Xenii1642/Xii-Boy-Pocket/STL/Buttons/R.stl

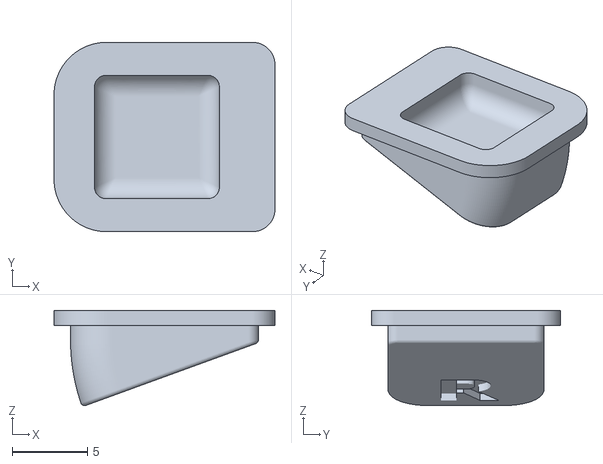
[picture p18: CAD file, 2024-10-31]
STL/Buttons/R.stl
14.7 x 12.6 x 6.34
