Xenii1642/Xii-Boy-Pocket/STL/Buttons/Volume.stl

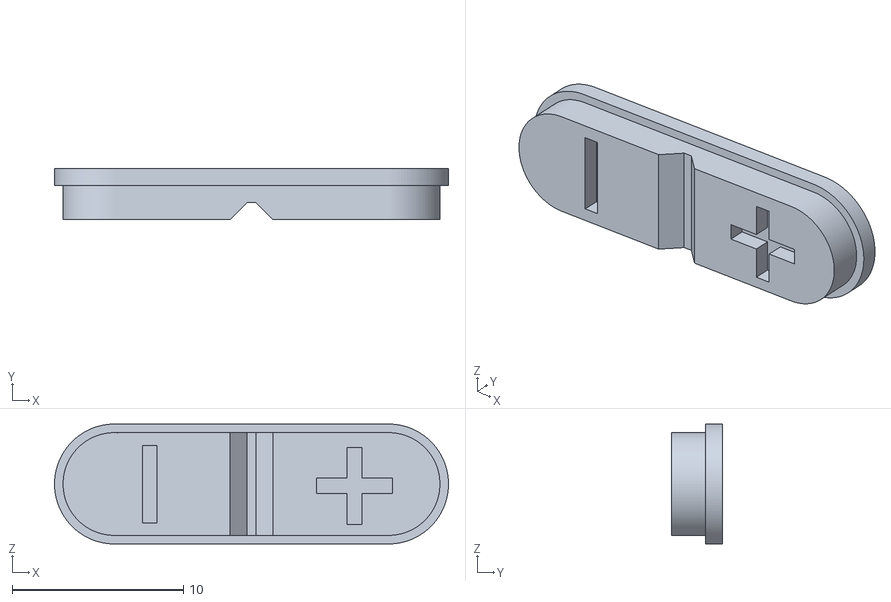
[picture p19: CAD file, 2024-10-31]
STL/Buttons/Volume.stl
23.0 x 3.00 x 7.00
