Xenii1642/Xii-Boy-Pocket/STL/Buttons/Power.stl

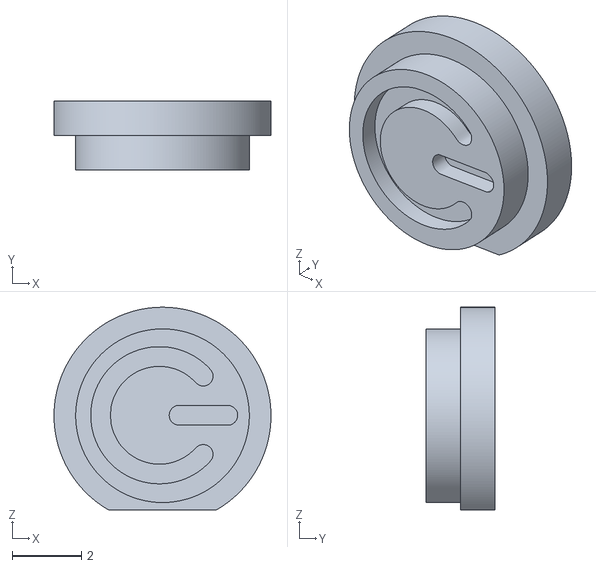
[picture p20: CAD file, 2024-10-31]
STL/Buttons/Power.stl
6.25 x 2.00 x 5.83
